cemergin/Adventures-on-the-Wheels-of-Steel/Images/completed2.jpg

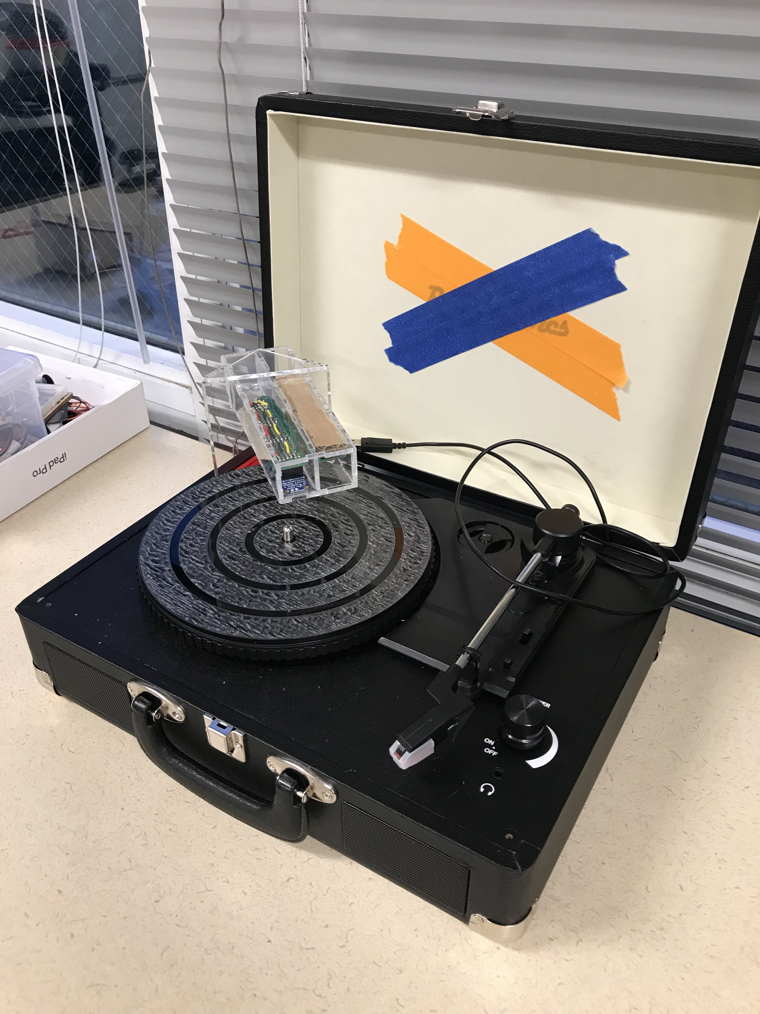
Images/completed2.jpg
