cemergin/Adventures-on-the-Wheels-of-Steel/Images/completed3.jpg

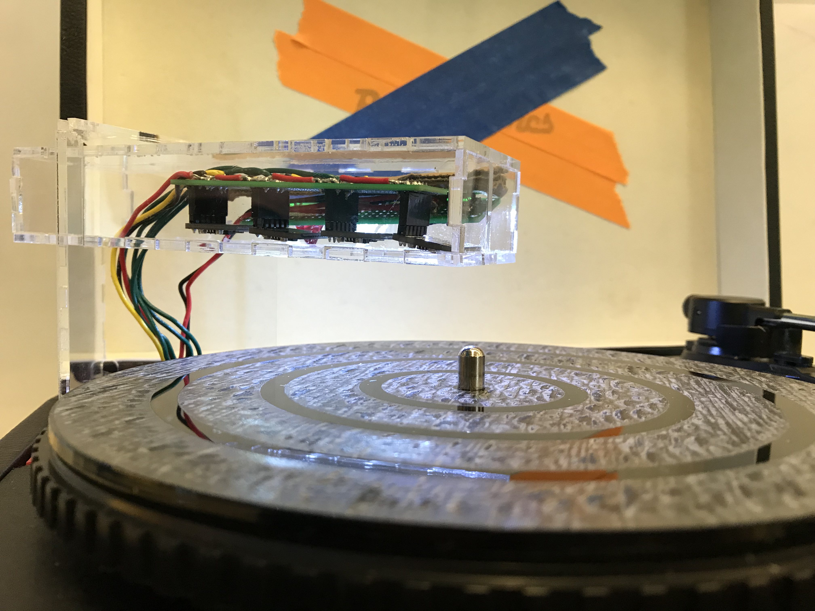
Images/completed3.jpg
