cemergin/Adventures-on-the-Wheels-of-Steel/Images/completed4.jpg

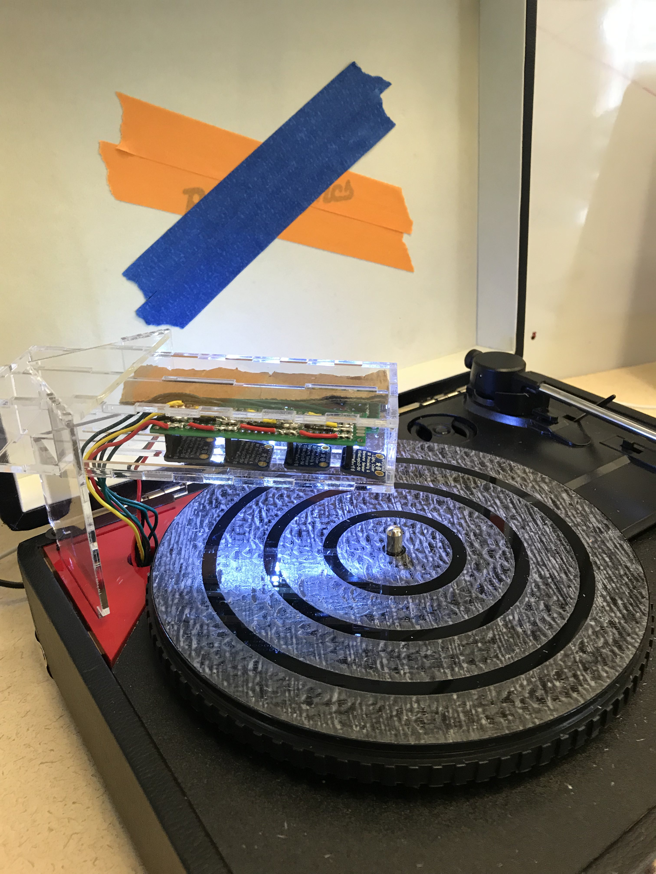
Images/completed4.jpg
