cemergin/Adventures-on-the-Wheels-of-Steel/Images/completed5.jpg

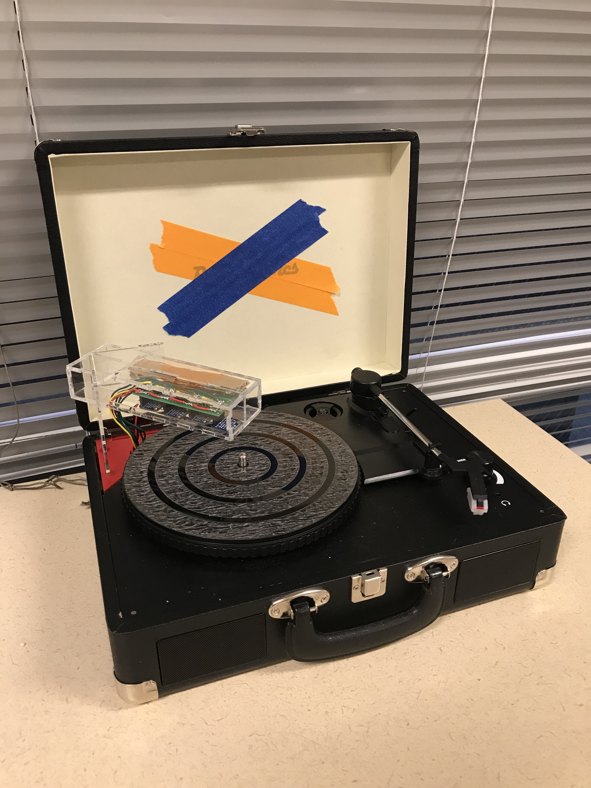
Images/completed5.jpg
