cemergin/Adventures-on-the-Wheels-of-Steel/Images/completed6.jpg

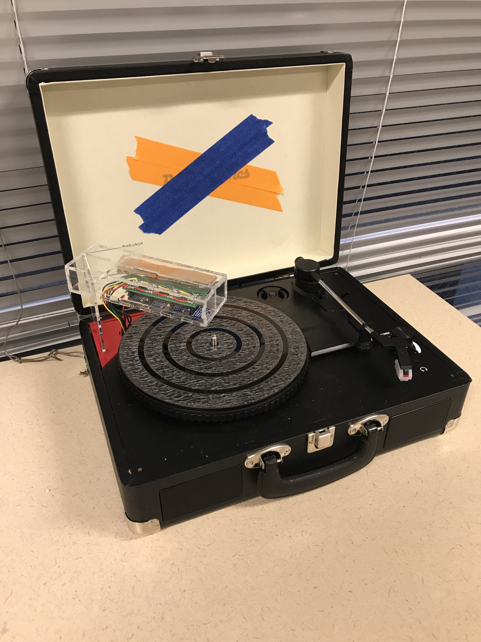
Images/completed6.jpg
