cemergin/Adventures-on-the-Wheels-of-Steel/Images/tonearm1.JPG

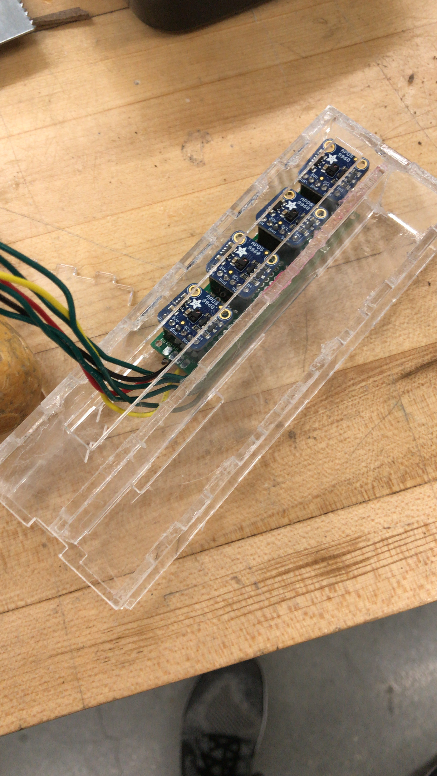
Images/tonearm1.JPG
