cemergin/Adventures-on-the-Wheels-of-Steel/Images/tonearm2.JPG

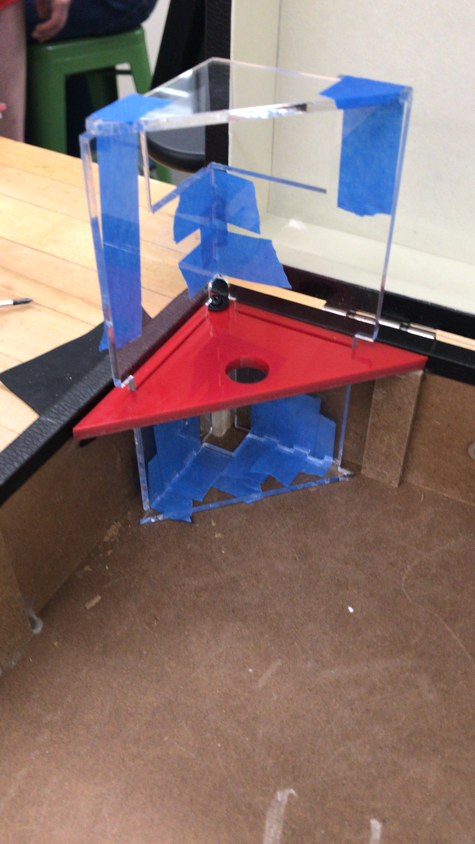
Images/tonearm2.JPG
