cemergin/Adventures-on-the-Wheels-of-Steel/Images/tonearm3.JPG

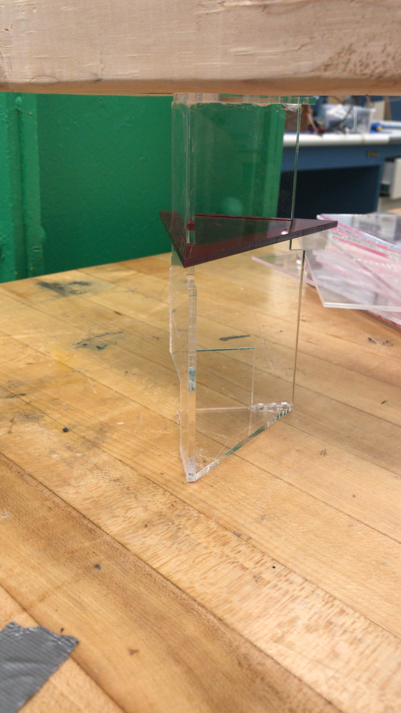
Images/tonearm3.JPG
