cemergin/Adventures-on-the-Wheels-of-Steel/Images/tonearm4.JPG

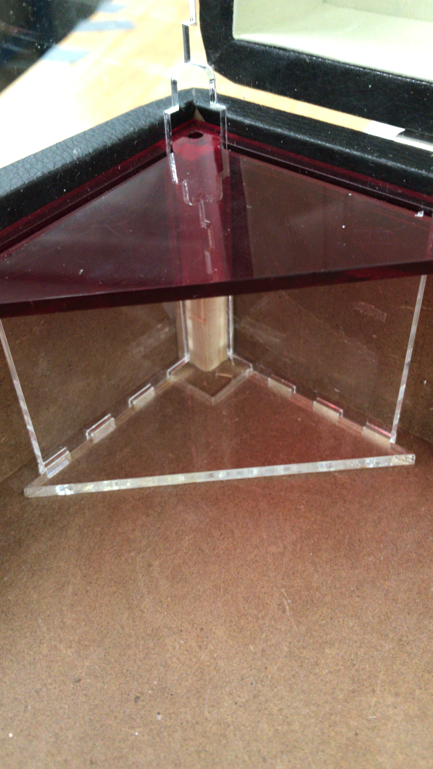
Images/tonearm4.JPG
