cemergin/Adventures-on-the-Wheels-of-Steel/Tutorials/img/female.png

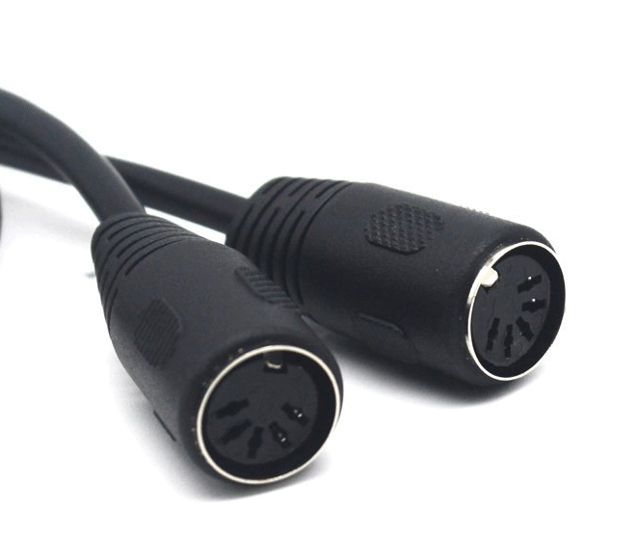
Tutorials/img/female.png
